Whackalenso/CircuitSax/models/11_Bis.stl

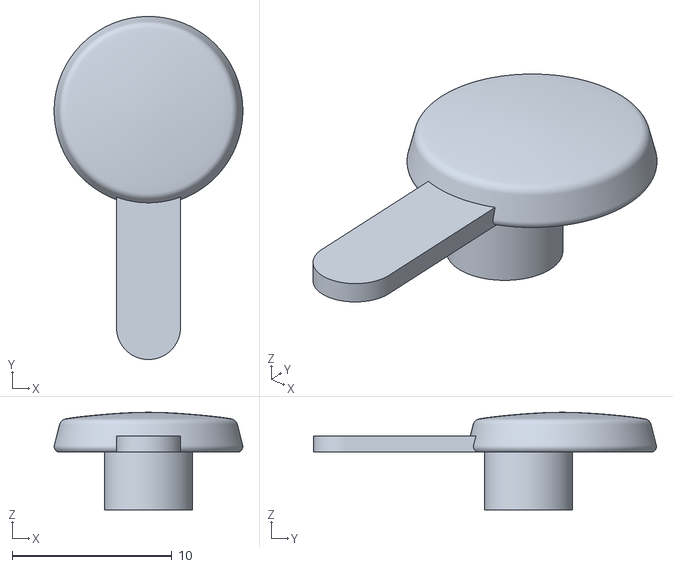
[picture p33: CAD file, 2024-10-20]
models/11_Bis.stl
11.8 x 21.5 x 6.10
