Whackalenso/CircuitSax/models/6_C.stl

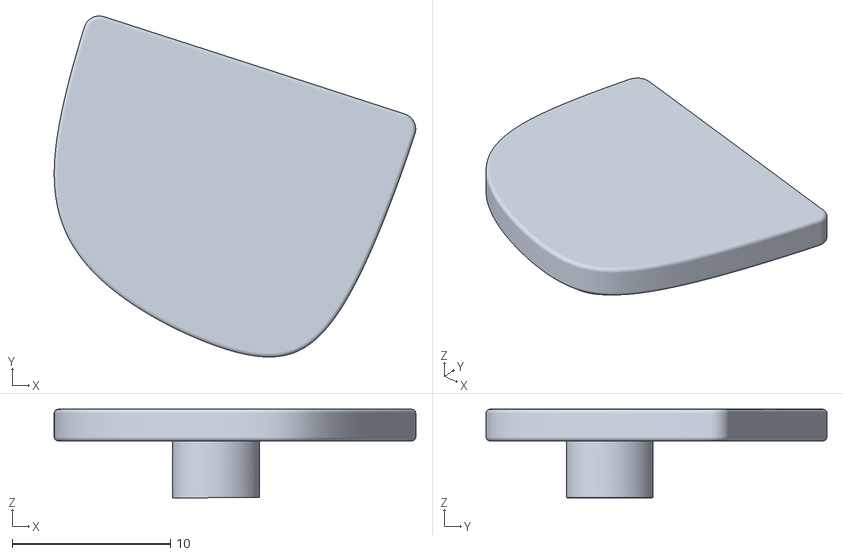
[picture p34: CAD file, 2024-10-20]
models/6_C.stl
22.9 x 21.6 x 5.60
