Whackalenso/CircuitSax/models/14_SK1.stl

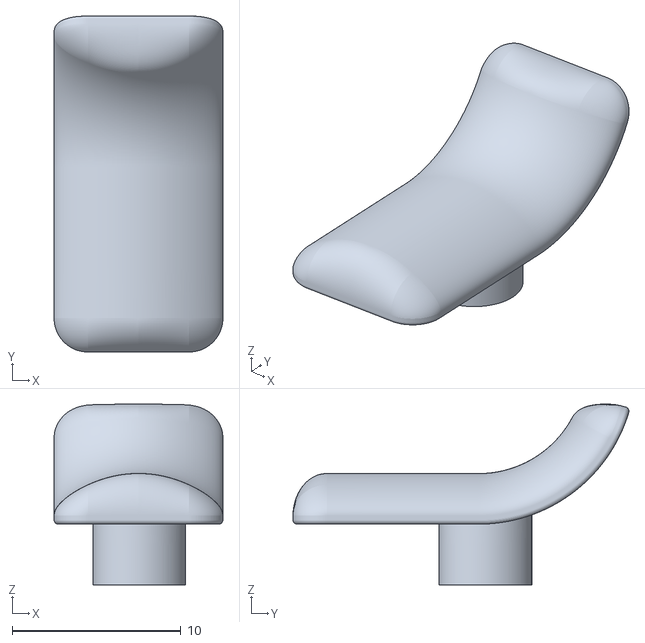
[picture p35: CAD file, 2024-10-20]
models/14_SK1.stl
10.0 x 19.9 x 10.7
