Whackalenso/CircuitSax/models/7_PK1.stl

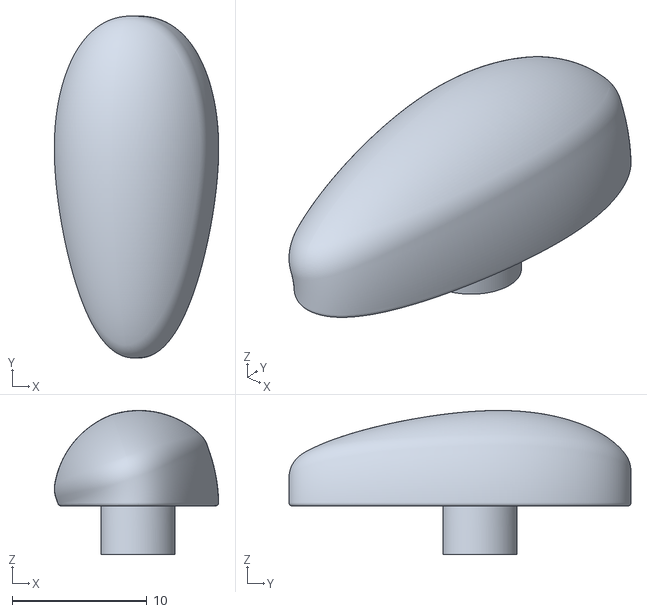
[picture p36: CAD file, 2024-10-20]
models/7_PK1.stl
12.2 x 25.4 x 10.7
