Whackalenso/CircuitSax/images/pcb.jpg

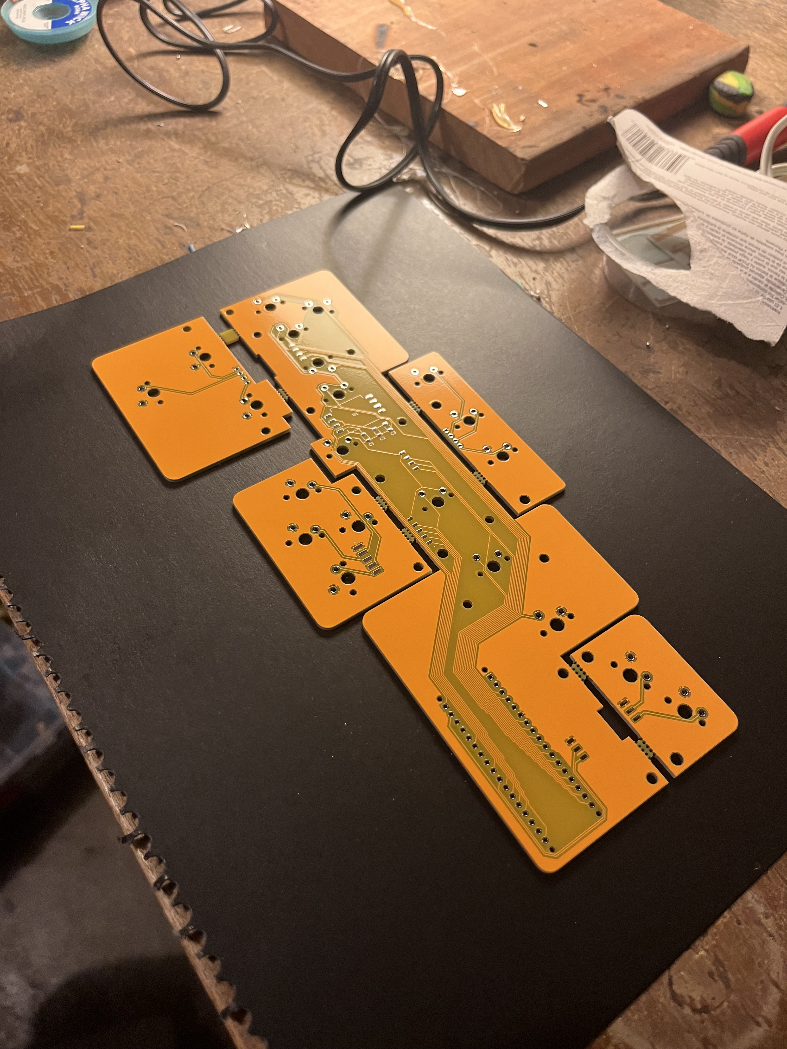
images/pcb.jpg
